Absurd-Industries/sanctury-os/images/CrMlKa04.jpg

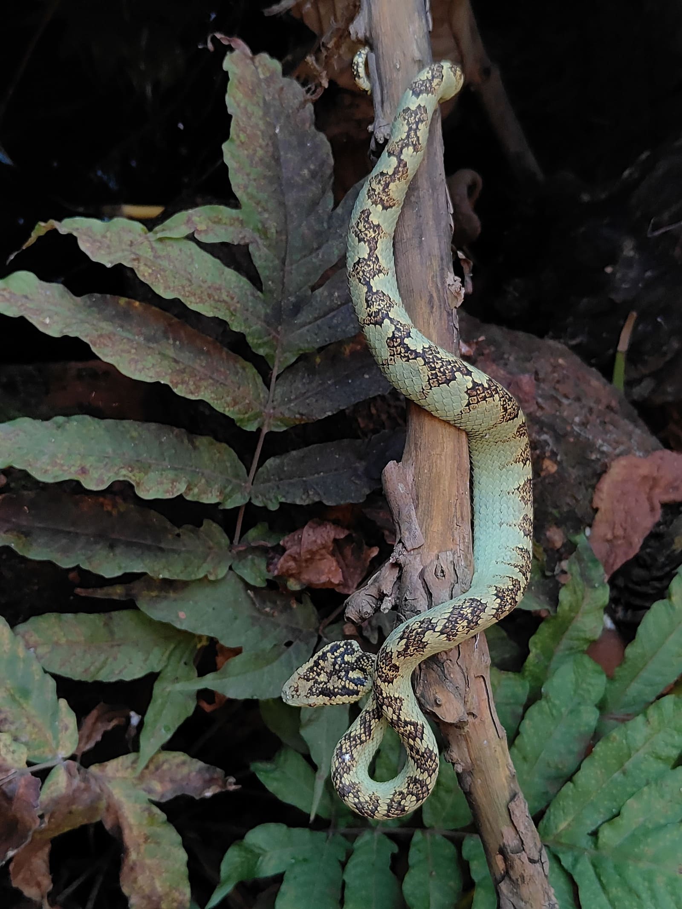
images/CrMlKa04.jpg
