Absurd-Industries/sanctury-os/images/DaRuKa01.jpg

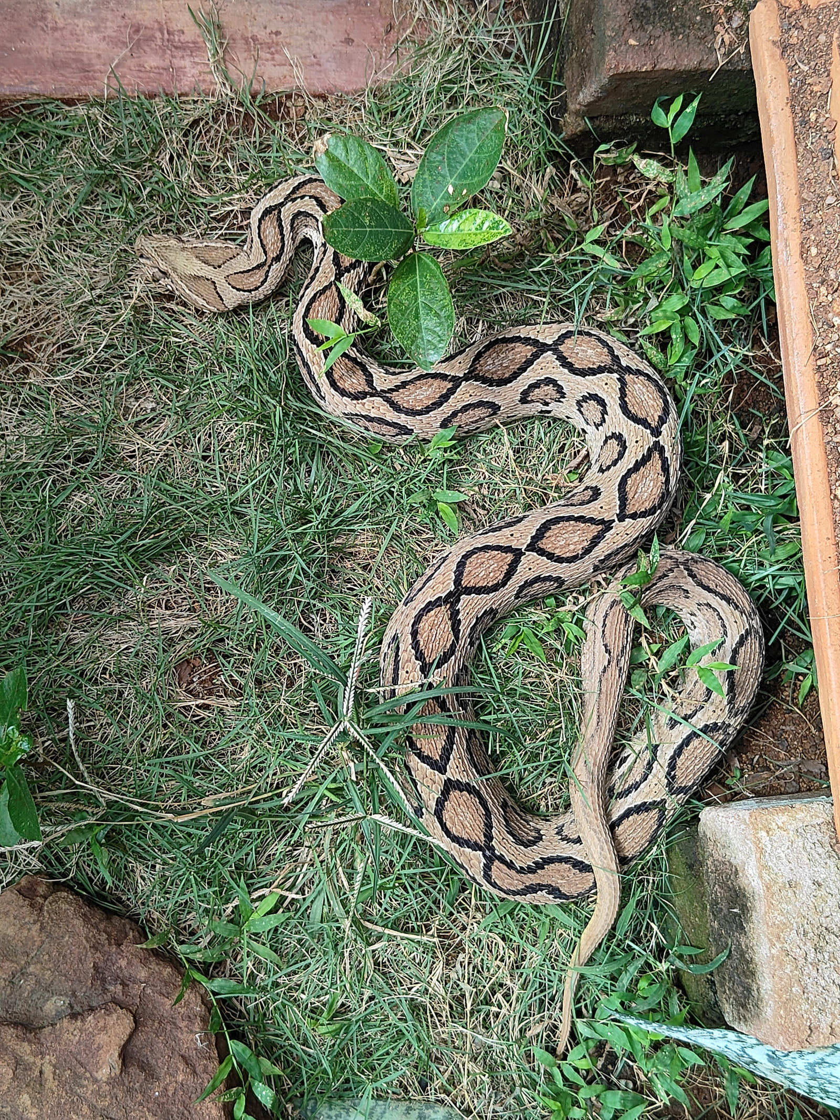
images/DaRuKa01.jpg
