Absurd-Industries/sanctury-os/images/DaRuKa02.jpg

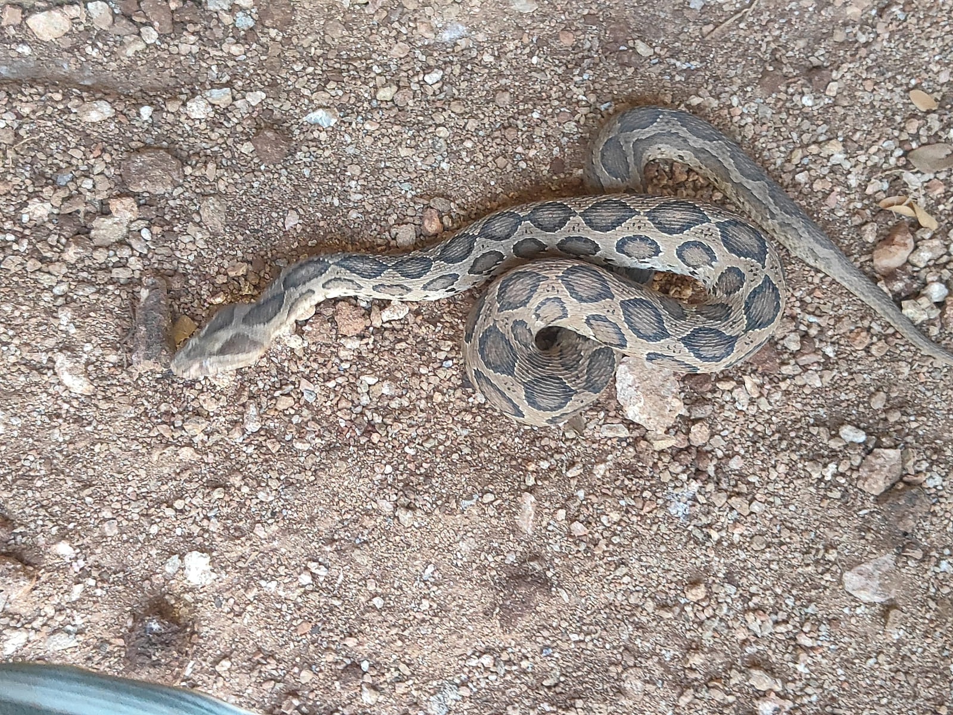
images/DaRuKa02.jpg
