Absurd-Industries/sanctury-os/images/DaRuKa03.jpg

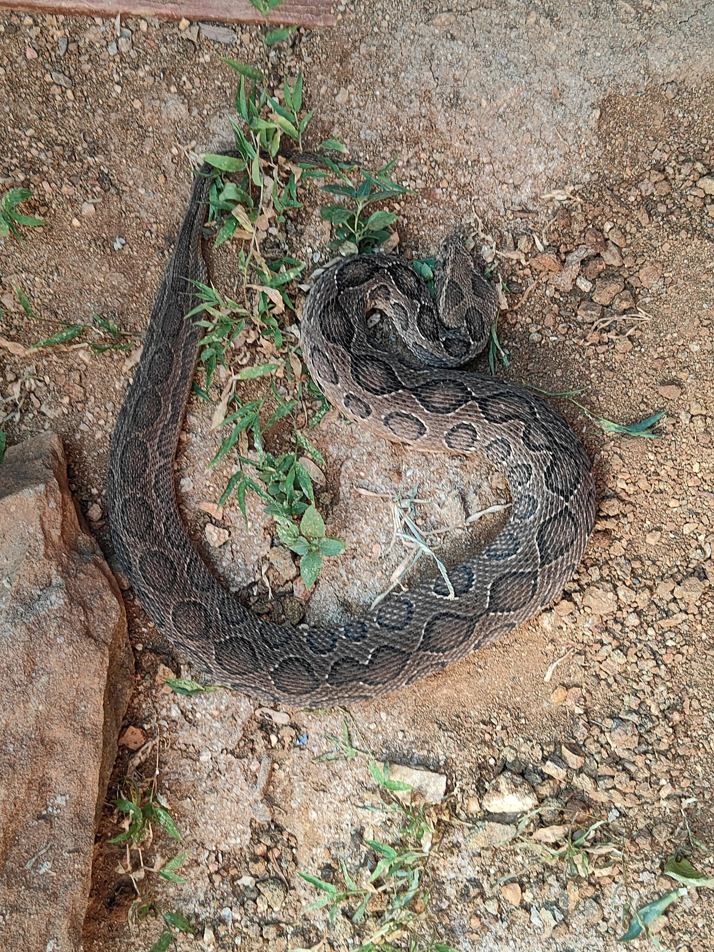
images/DaRuKa03.jpg
