Absurd-Industries/sanctury-os/images/DaRuKa04.jpg

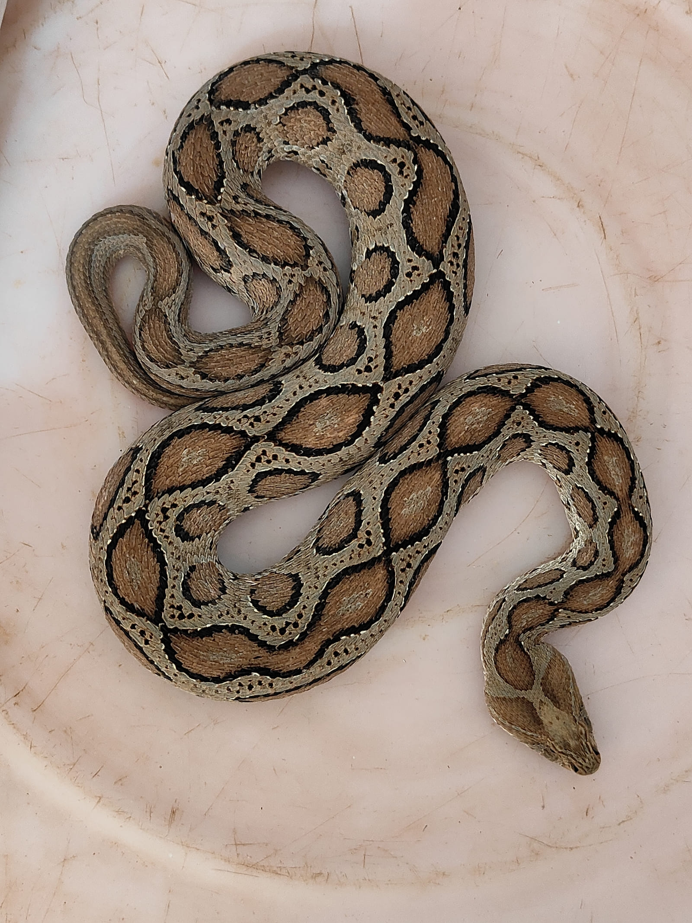
images/DaRuKa04.jpg
