Absurd-Industries/sanctury-os/images/DaRuKa06.jpg

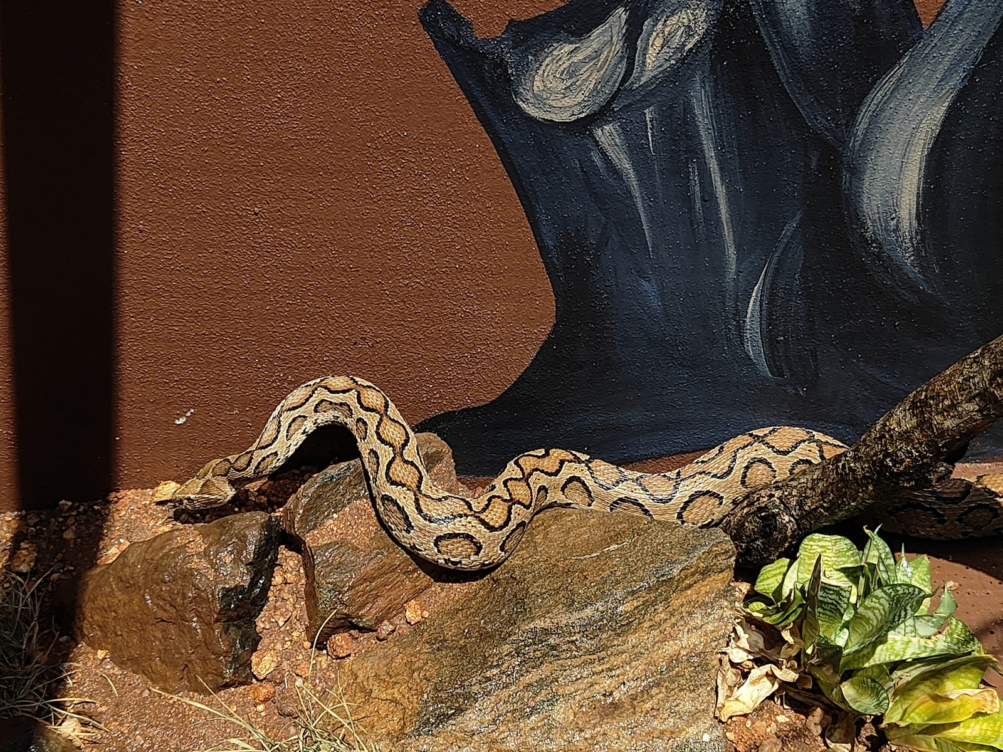
images/DaRuKa06.jpg
