Absurd-Industries/sanctury-os/images/EcCaKa02.jpg

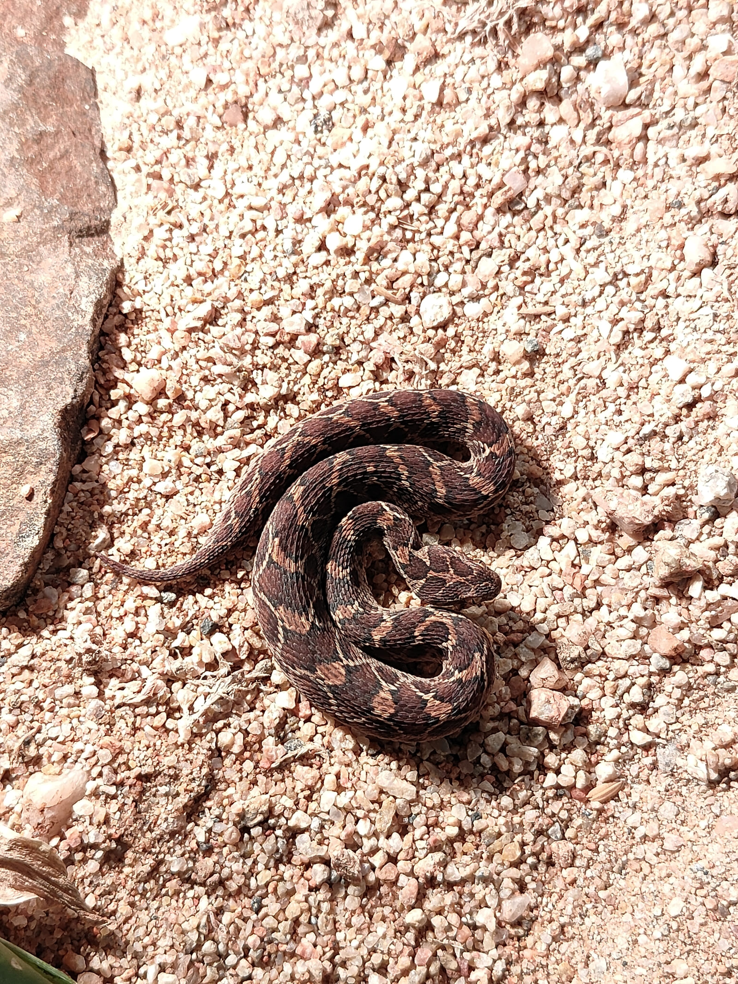
images/EcCaKa02.jpg
