Absurd-Industries/sanctury-os/images/EcCaKa03.jpg

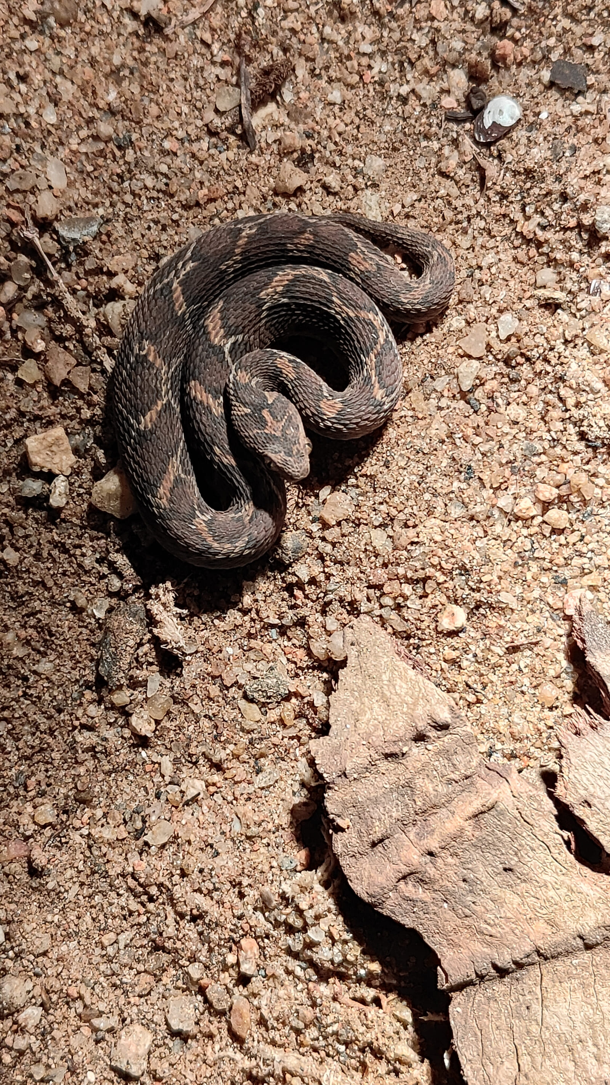
images/EcCaKa03.jpg
