Absurd-Industries/sanctury-os/images/EcCaKa04.jpg

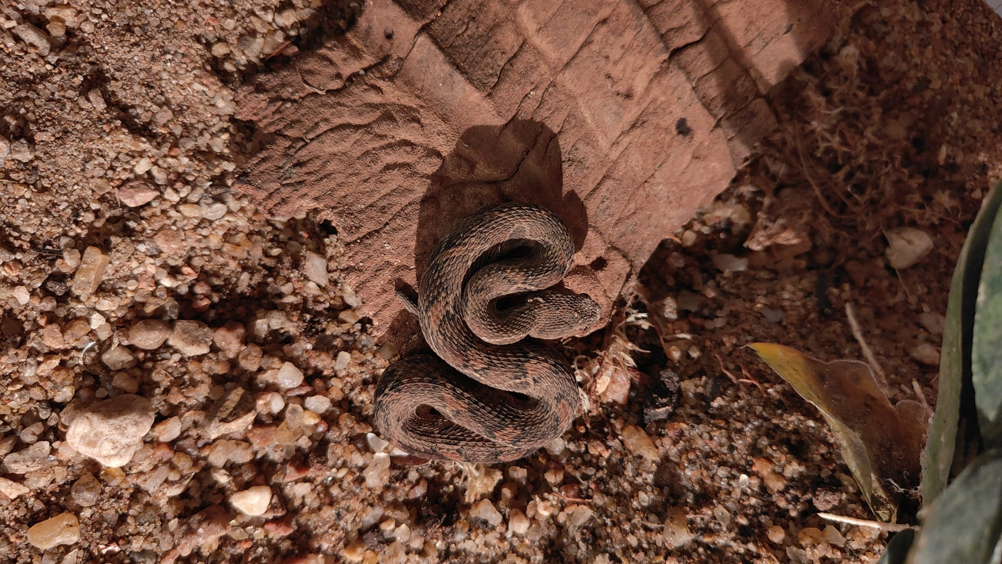
images/EcCaKa04.jpg
