Absurd-Industries/sanctury-os/images/HyHyKa02.jpg

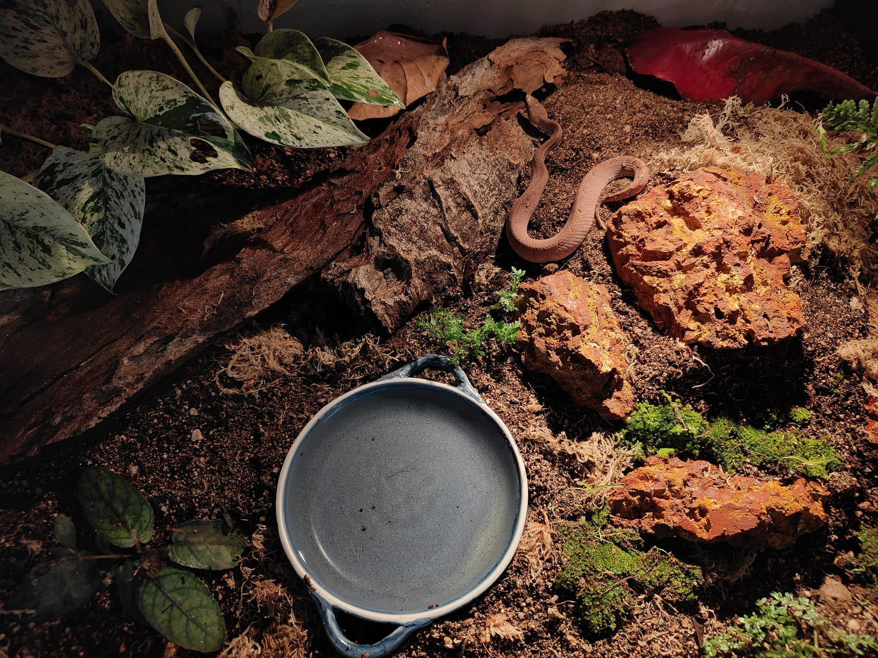
images/HyHyKa02.jpg
