Absurd-Industries/sanctury-os/images/HyHyKa03.jpg

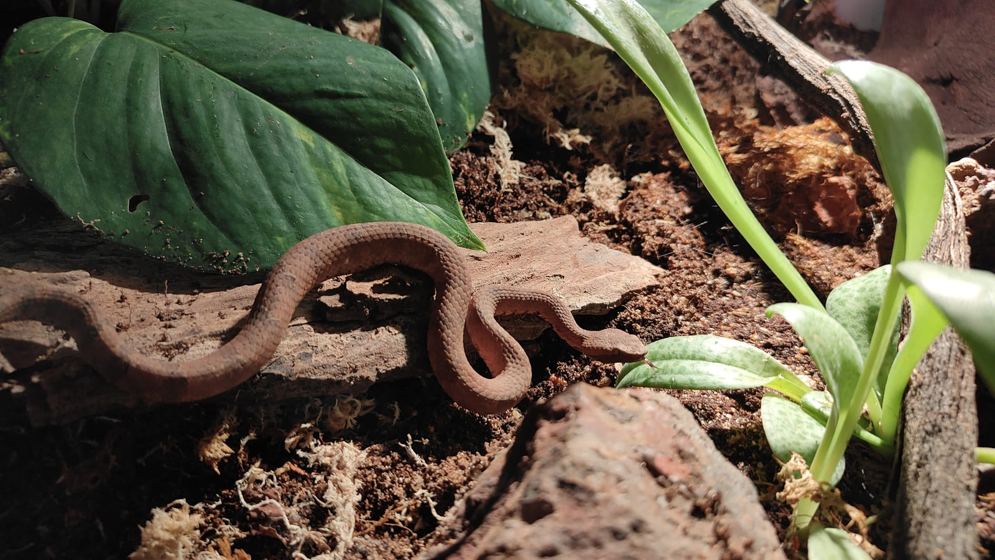
images/HyHyKa03.jpg
