Absurd-Industries/sanctury-os/images/OpKaKa01.jpg

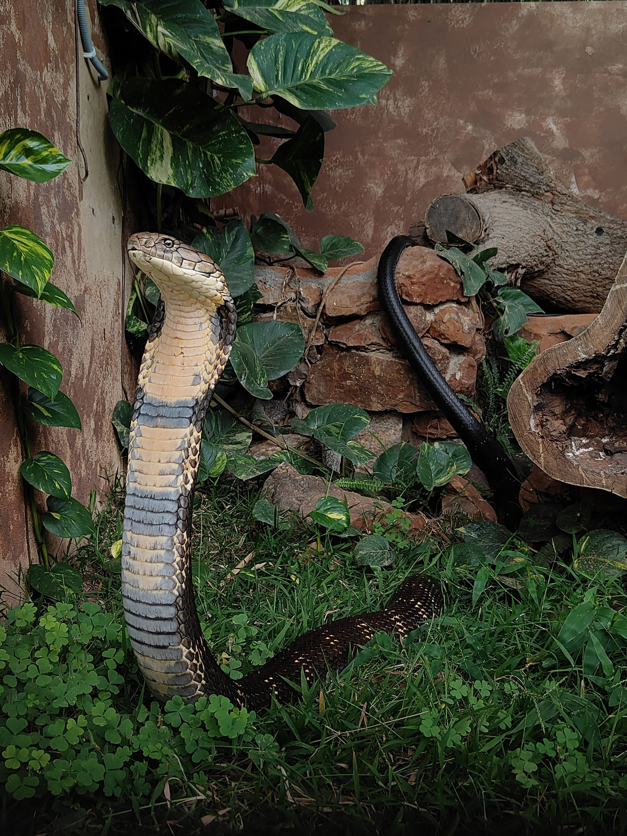
images/OpKaKa01.jpg
