Absurd-Industries/sanctury-os/images/OpKaKa02.jpg

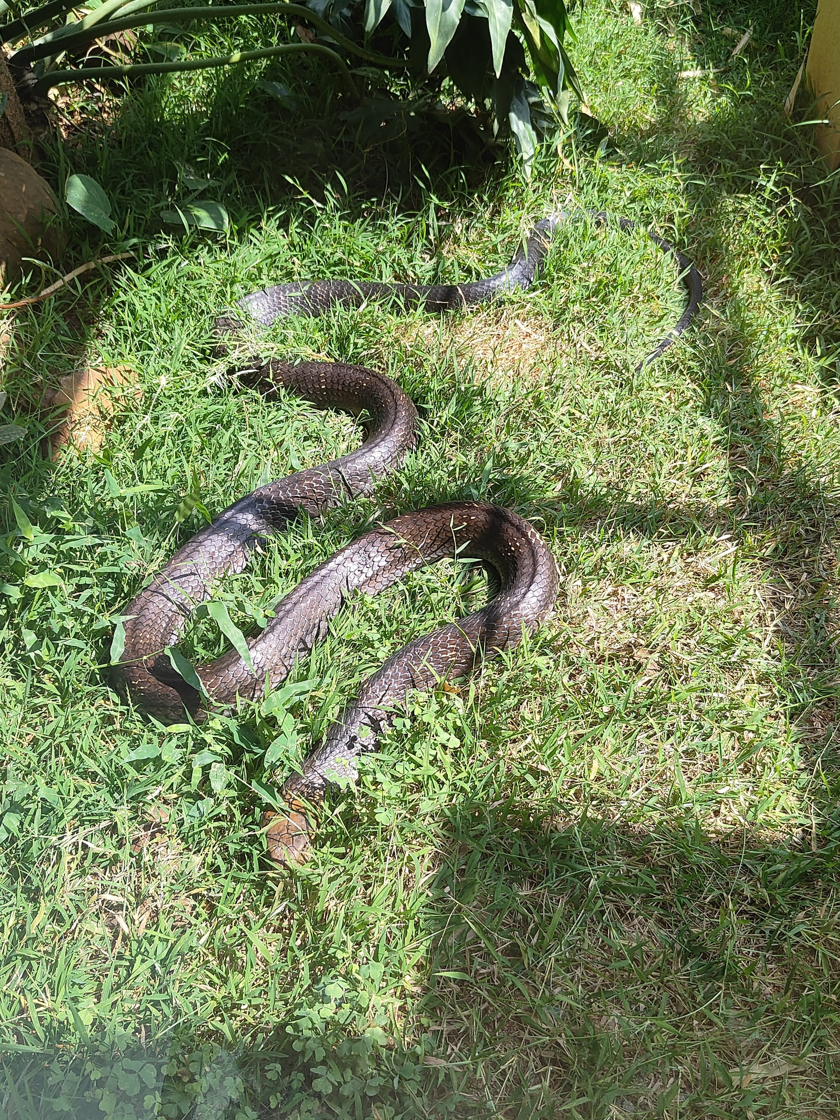
images/OpKaKa02.jpg
